mdumas2/development-board-with-PIC32-project/CODE/PBL2.X/alarme.h

/* 
 * File:   alarme.h
 * Author: mateu
 *
 * Created on 12 de Outubro de 2019, 17:54
 */

#ifndef ALARME_H
#define	ALARME_H

#ifdef	__cplusplus
extern "C" {
#endif




#ifdef	__cplusplus
}
#endif

void Alarme1Tst(void);
void Alarme2Tst(void);

#endif	/* ALARME_H */
