mdumas2/development-board-with-PIC32-project/CODE/PBL2.X/EnviaSerial.h

/* 
 * File:   EnviaSerial.h
 * Author: GUILH
 *
 * Created on 23 de Outubro de 2019, 20:18
 */

#ifndef ENVIASERIAL_H
#define	ENVIASERIAL_H

#ifdef	__cplusplus
extern "C" {
#endif




#ifdef	__cplusplus
}
#endif

void Envia_Valores_Serial(void);

#endif	/* ENVIASERIAL_H */
