mdumas2/development-board-with-PIC32-project/CODE/PBL2.X/adc.h

/* 
 * File:   adc.h
 * Author: mateu
 *
 * Created on 12 de Outubro de 2019, 18:34
 */

#ifndef ADC_H
#define	ADC_H

#ifdef	__cplusplus
extern "C" {
#endif




#ifdef	__cplusplus
}
#endif

unsigned int adcRead_Teclado(void);
unsigned int adcRead1(void);
unsigned int adcRead2(void);


#endif	/* ADC_H */
