mdumas2/development-board-with-PIC32-project/CODE/PBL2.X/delay.h

/* 
 * File:   delay.h
 * Author: GUILH
 *
 * Created on 12 de Outubro de 2019, 16:29
 */

#ifndef DELAY_H
#define	DELAY_H

#ifdef	__cplusplus
extern "C" {
#endif




#ifdef	__cplusplus
}
#endif

#endif	/* DELAY_H */
