mdumas2/development-board-with-PIC32-project/CODE/PBL2.X/delay_1.h

/* 
 * File:   delay_1.h
 * Author: GUILH
 *
 * Created on 12 de Outubro de 2019, 16:30
 */

#ifndef DELAY_1_H
#define	DELAY_1_H

#ifdef	__cplusplus
extern "C" {
#endif




#ifdef	__cplusplus
}
#endif

void Delay10us(uint32_t delay);
void DelayMiliS(uint16_t ms);

#endif	/* DELAY_1_H */
