mdumas2/development-board-with-PIC32-project/CODE/PBL2.X/lm35.h

/* 
 * File:   lm35.h
 * Author: GUILH
 *
 * Created on October 11, 2019, 6:01 PM
 */

#ifndef LM35_H
#define	LM35_H

#ifdef	__cplusplus
extern "C" {
#endif




#ifdef	__cplusplus
}
#endif
void temperatura_LM35(void);
void gas_sensor(void);
void temperatura_LM35_display(void);

#endif	/* LM35_H */
