mdumas2/development-board-with-PIC32-project/CODE/PBL2.X/output.h

/* 
 * File:   output.h
 * Author: mateu
 *
 * Created on 12 de Outubro de 2019, 18:19
 */

#ifndef OUTPUT_H
#define	OUTPUT_H

#ifdef	__cplusplus
extern "C" {
#endif




#ifdef	__cplusplus
}
#endif

void outputInit(void);
void outputPrint(int numTela, int idioma);

#endif	/* OUTPUT_H */
